Larkuo/undergrad-capstone/Design/CAD Model/cad images/cad_base.png

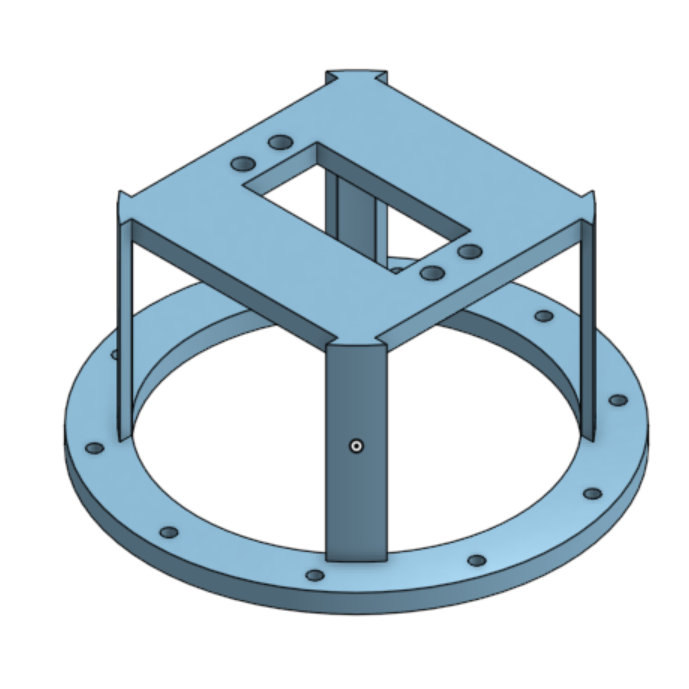
Design/CAD Model/cad images/cad_base.png
