Larkuo/undergrad-capstone/Design/CAD Model/cad images/cad_link_1.png

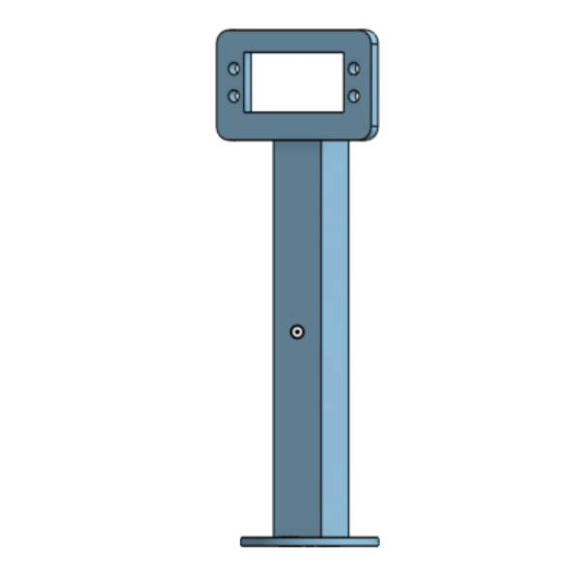
Design/CAD Model/cad images/cad_link_1.png
