Larkuo/undergrad-capstone/Design/CAD Model/cad images/cad_servo.png

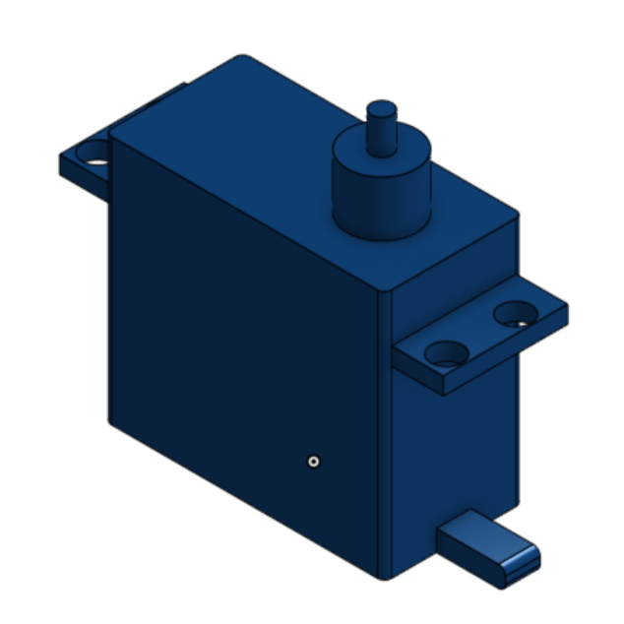
Design/CAD Model/cad images/cad_servo.png
