Larkuo/undergrad-capstone/Prototyping/Media/raspi screen grab 2.PNG

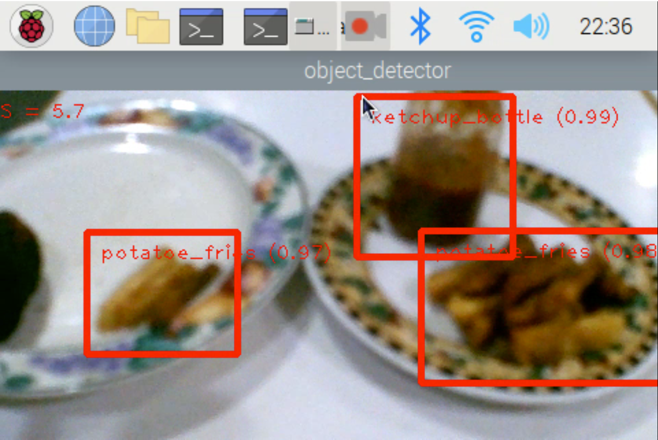
Prototyping/Media/raspi screen grab 2.PNG
