Larkuo/undergrad-capstone/Design/CAD Model/Parts to Print/Camera Stand/Camera Base C.stl

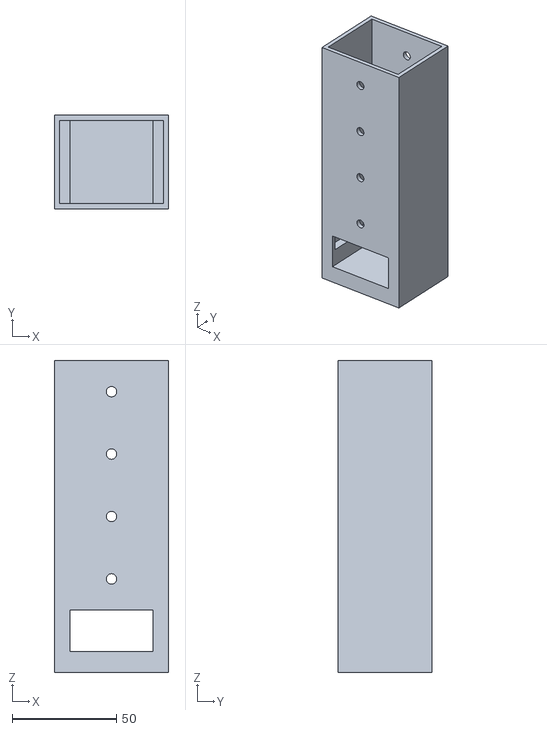
[picture p40: CAD file, 2022-05-13]
Design/CAD Model/Parts to Print/Camera Stand/Camera Base C.stl
55.0 x 45.0 x 150.0
