Larkuo/undergrad-capstone/Design/CAD Model/CAD Final/Joint Servo.stl

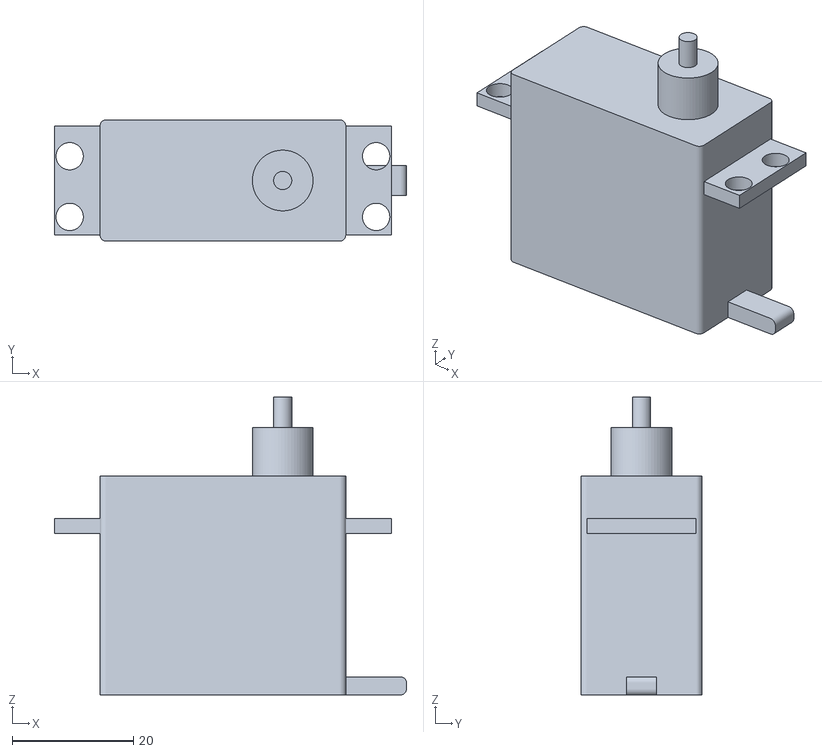
[picture p41: CAD file, 2022-05-13]
Design/CAD Model/CAD Final/Joint Servo.stl
58.0 x 20.0 x 49.1
