Larkuo/undergrad-capstone/Design/CAD Model/Parts to Print - V3/Link 1.stl

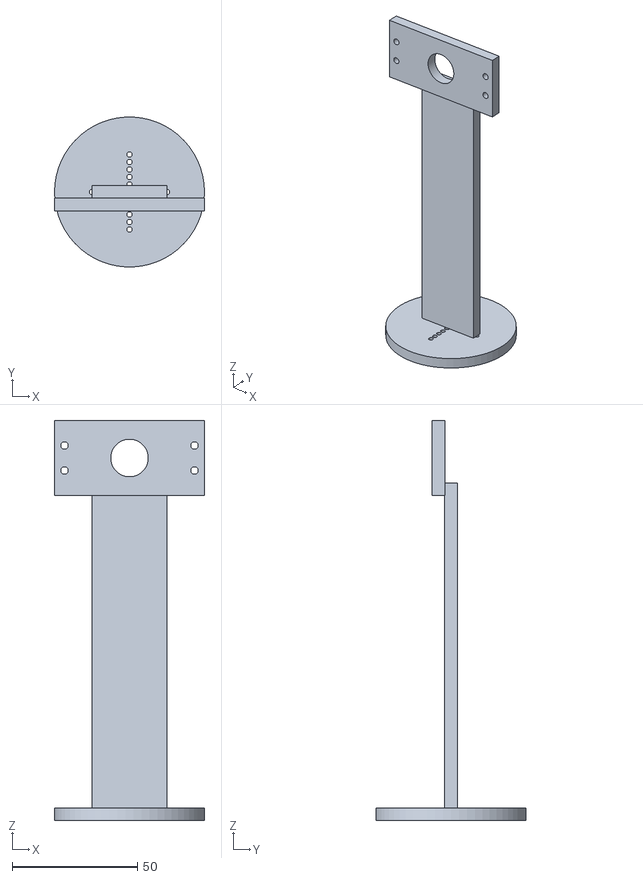
[picture p42: CAD file, 2022-05-13]
Design/CAD Model/Parts to Print - V3/Link 1.stl
60.0 x 59.9 x 160.0
