Larkuo/undergrad-capstone/Design/CAD Model/Parts to Print/Arm/Base Slab (Raspberry Pi).stl

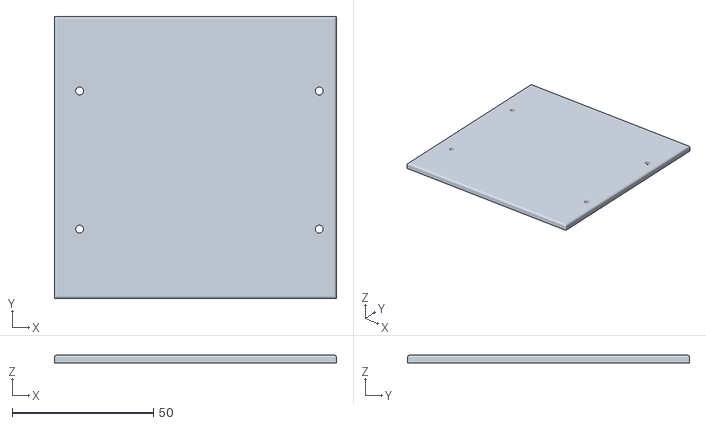
[picture p43: CAD file, 2022-05-13]
Design/CAD Model/Parts to Print/Arm/Base Slab (Raspberry Pi).stl
100.0 x 100.0 x 3.00
