Larkuo/undergrad-capstone/Design/CAD Model/CAD Final/Link 1.stl

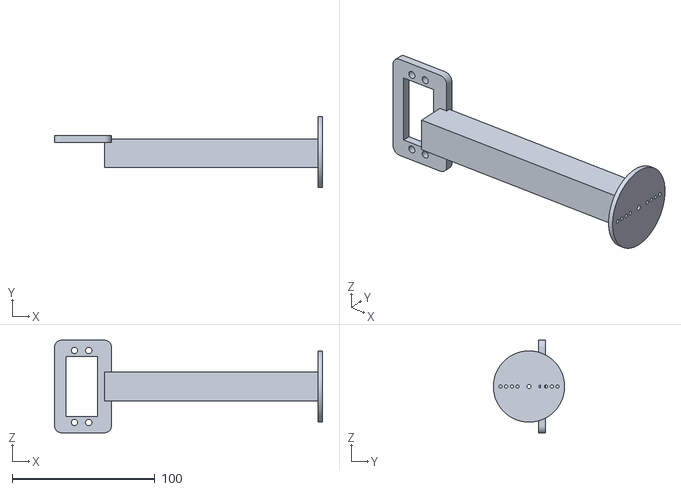
[picture p44: CAD file, 2022-05-13]
Design/CAD Model/CAD Final/Link 1.stl
188.0 x 49.9 x 65.0
