Larkuo/undergrad-capstone/Prototyping/Scripts/camera calibration images/WIN_20220427_16_50_57_Pro.jpg

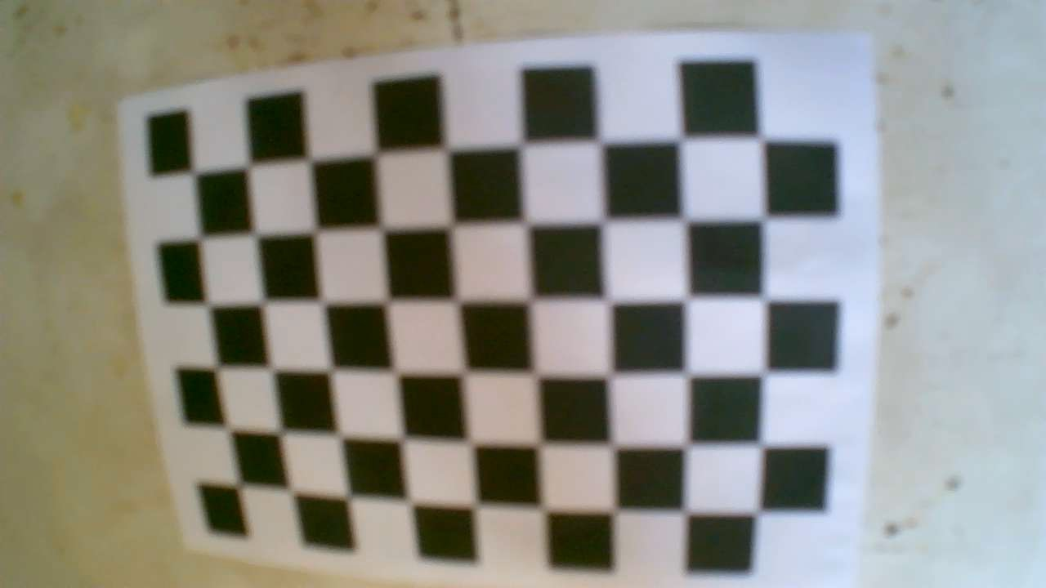
Prototyping/Scripts/camera calibration images/WIN_20220427_16_50_57_Pro.jpg
