Larkuo/undergrad-capstone/Prototyping/Scripts/camera calibration images/WIN_20220427_16_51_49_Pro.jpg

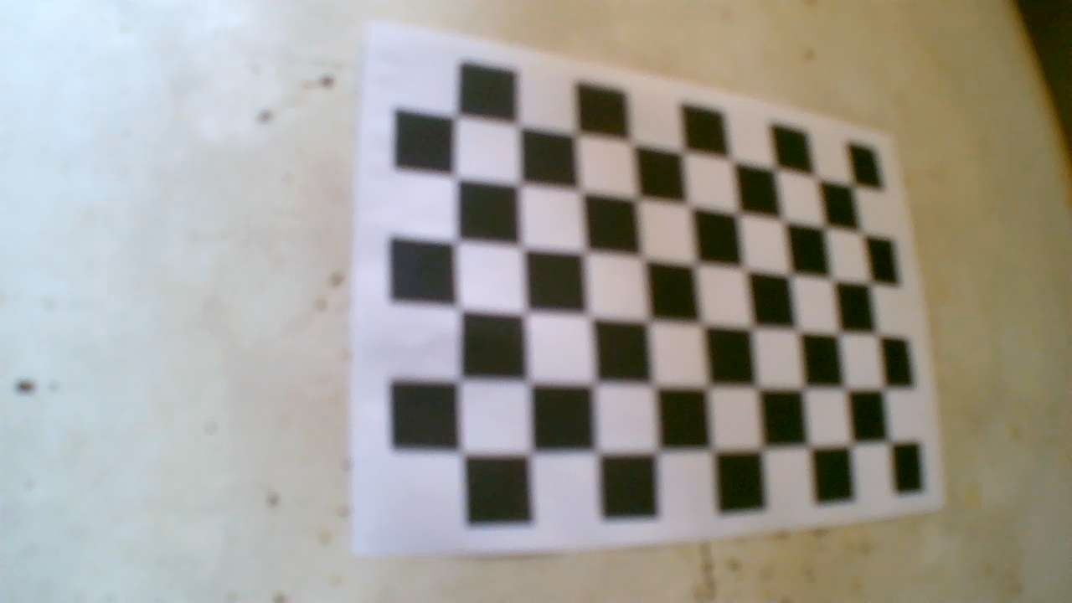
Prototyping/Scripts/camera calibration images/WIN_20220427_16_51_49_Pro.jpg
