Larkuo/undergrad-capstone/Prototyping/Scripts/camera calibration images/WIN_20220427_16_52_03_Pro.jpg

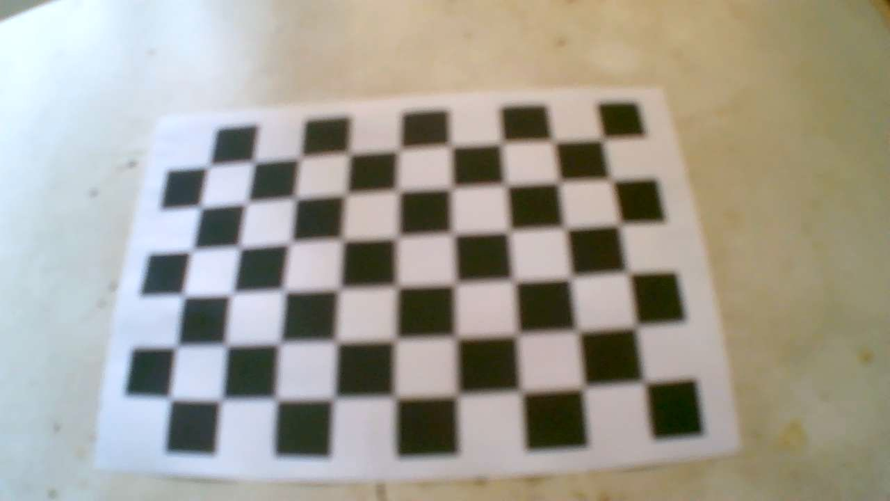
Prototyping/Scripts/camera calibration images/WIN_20220427_16_52_03_Pro.jpg
